tristandijkstra/OpenGimbal/CAD/TableTop/TableTopV/ring_2_quater_X3.SLDPRT

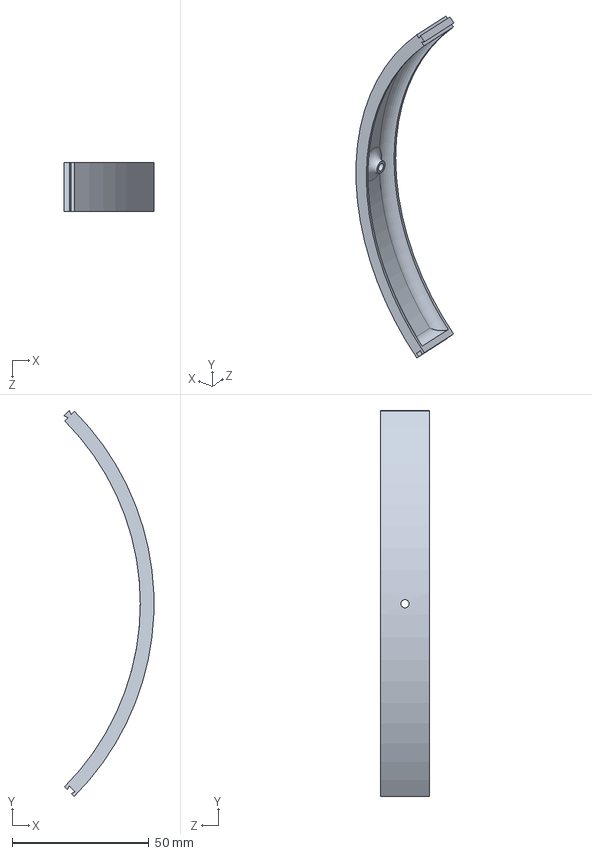
[picture p19: CAD file, 2023-06-18]
CAD/TableTop/TableTopV/ring_2_quater_X3.SLDPRT
32.9 x 140.9 x 18.0 mm
