tristandijkstra/OpenGimbal/CAD/TableTop/STL/ring_2_foot.STL

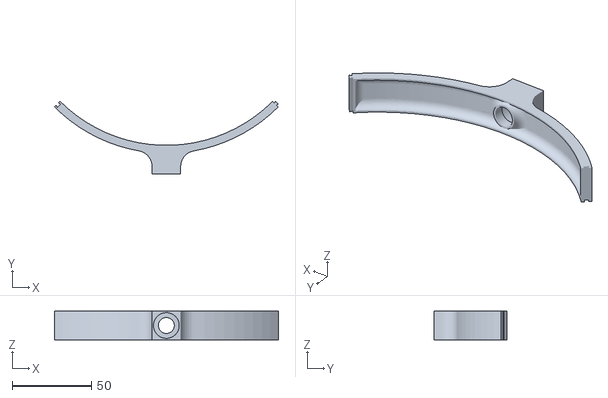
[picture p20: CAD file, 2023-06-18]
CAD/TableTop/STL/ring_2_foot.STL
140.9 x 45.9 x 18.0
