tristandijkstra/OpenGimbal/CAD/TableTop/TableTopV/base_8mm_bearing_version/base_merged_for_8mm_bearing_spacer.SLDPRT

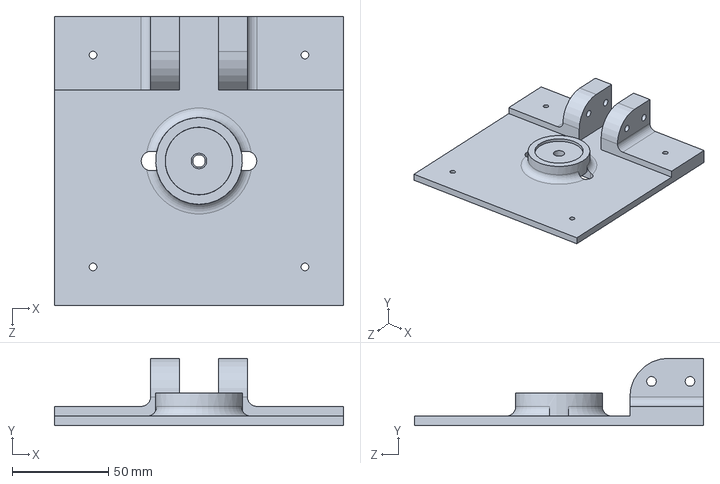
[picture p21: CAD file, 2023-06-18]
CAD/TableTop/TableTopV/base_8mm_bearing_version/base_merged_for_8mm_bearing_spacer.SLDPRT
150.0 x 35.0 x 150.0 mm
