tristandijkstra/OpenGimbal/CAD/TableTop/STL/ring_1_quater_X4.STL

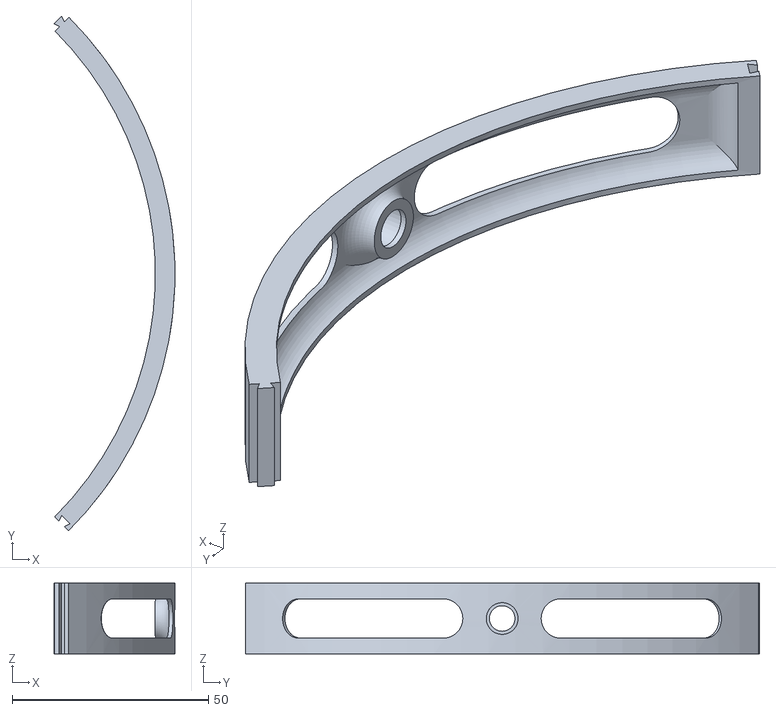
[picture p22: CAD file, 2023-06-18]
CAD/TableTop/STL/ring_1_quater_X4.STL
30.8 x 131.0 x 18.0
